alextrof94/SiGameIRL/v2/Models/Button/PartBottom.jpg

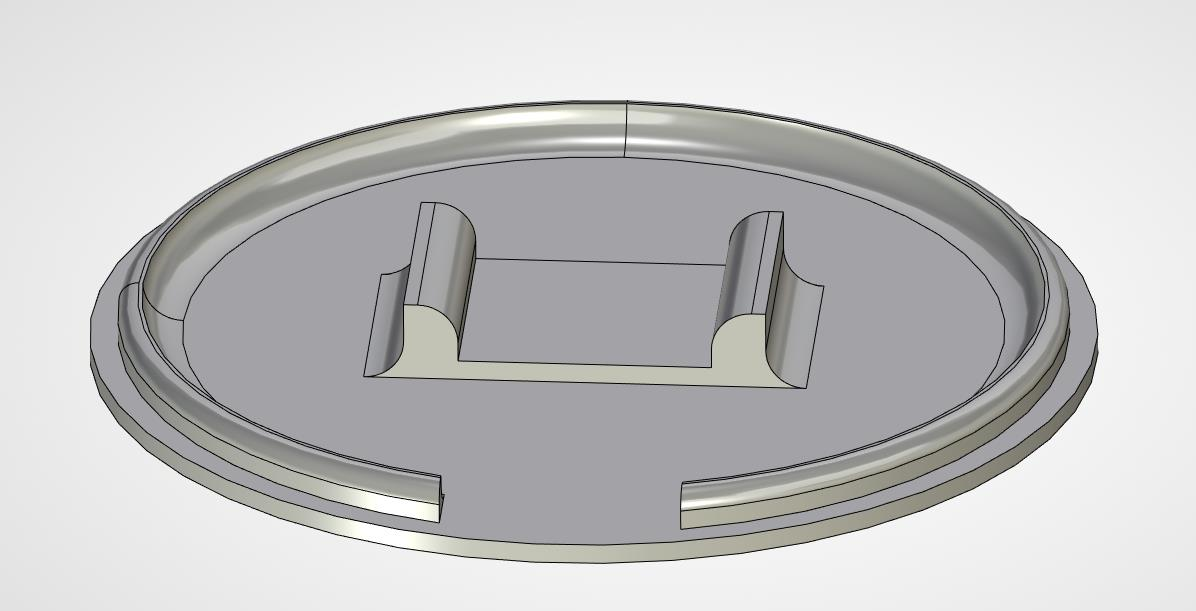
v2/Models/Button/PartBottom.jpg
