alextrof94/SiGameIRL/v2/Models/Button/PartTop.jpg

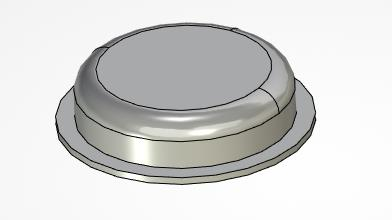
v2/Models/Button/PartTop.jpg
