alextrof94/SiGameIRL/v1/Models/Judge/SiGame_Judge_Accum.stl

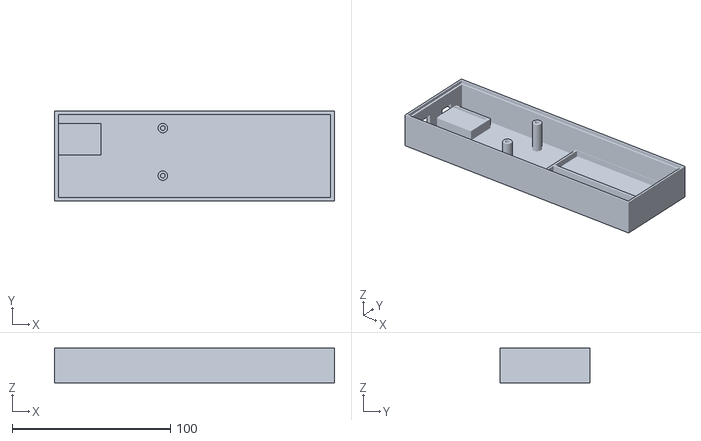
[picture p47: CAD file, 2020-06-23, an earlier design]
v1/Models/Judge/SiGame_Judge_Accum.stl
176.8 x 57.0 x 22.0
